jbobrow/MonTagger/Documentation/Images/projX_demo.jpg

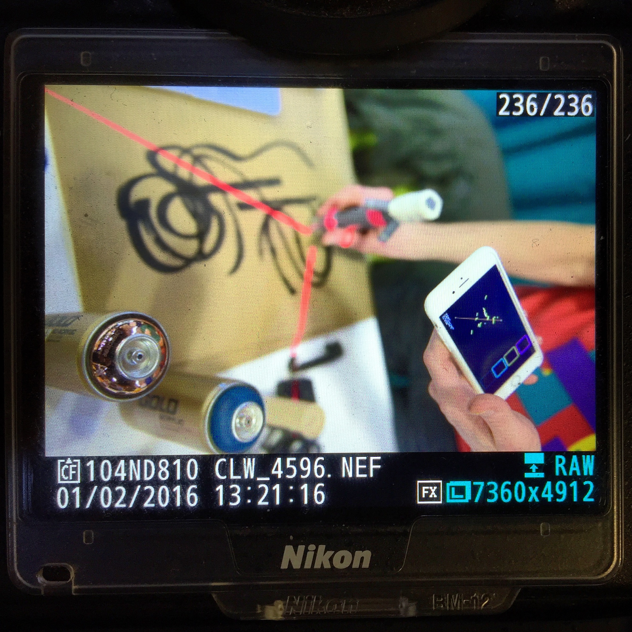
Documentation/Images/projX_demo.jpg
