jbobrow/MonTagger/MonTagger_iOS/bin/data/Default.png

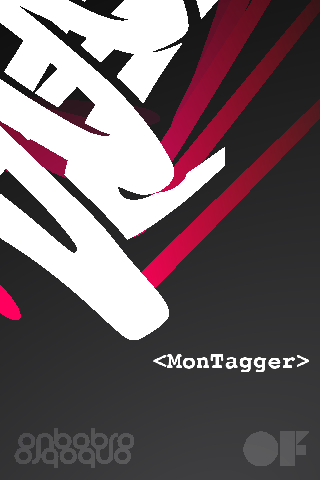
MonTagger_iOS/bin/data/Default.png
