jbobrow/MonTagger/MonTagger_iOS/bin/data/Default@2x.png

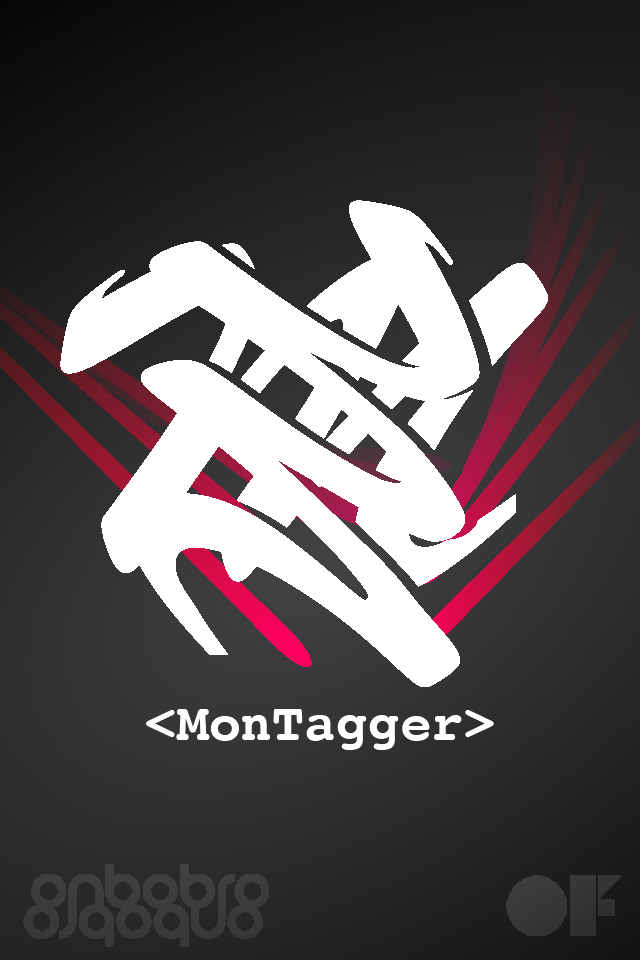
MonTagger_iOS/bin/data/Default@2x.png
