jbobrow/MonTagger/MonTagger_iOS/bin/data/Default@2x~iphone.png

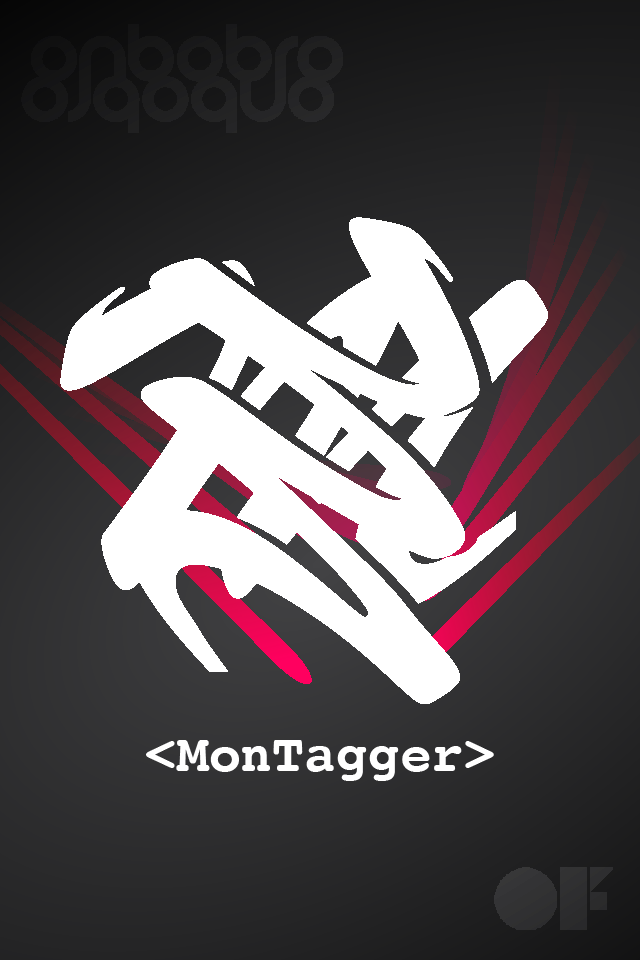
MonTagger_iOS/bin/data/Default@2x~iphone.png
