jbobrow/MonTagger/MonTagger_iOS/bin/data/Default~iphone.png

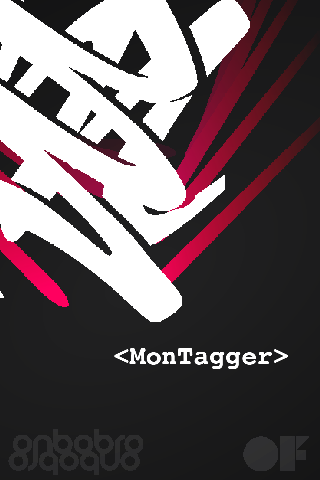
MonTagger_iOS/bin/data/Default~iphone.png
